sowec1-prog/litvinov-oled/include/team_logos.h

#pragma once
#include <Arduino.h>
constexpr uint8_t LOGO_W = 40;
constexpr uint8_t LOGO_H = 40;

static const uint8_t LOGO_TRI[] PROGMEM = {
  0x00, 0x20, 0x40, 0x18, 0x00, 0x00, 0x81, 0xC7,
  0x86, 0x00, 0x01, 0x11, 0xC7, 0x11, 0x00, 0x04,
  0x61, 0xE7, 0x1C, 0xC0, 0x08, 0x78, 0x00, 0x1C,
  0x20, 0x10, 0x30, 0x7C, 0x10, 0x10, 0x27, 0x03,
  0x01, 0x80, 0x10, 0x2D, 0x08, 0x00, 0x20, 0x08,
  0x4F, 0x30, 0x00, 0x98, 0xE4, 0x86, 0x40, 0x47,
  0x04, 0xF0, 0x80, 0x80, 0x4C, 0x02, 0xD2, 0x30,
  0x00, 0xFC, 0x62, 0x40, 0x39, 0x01, 0x7D, 0xC1,
  0x01, 0x72, 0x3F, 0xFF, 0x90, 0x9D, 0x72, 0x39,
  0xCF, 0xF0, 0x90, 0x00, 0x30, 0x3F, 0xF0, 0x10,
  0x01, 0xC3, 0xFB, 0x60, 0x40, 0x03, 0x86, 0x65,
  0xB4, 0x40, 0x0E, 0x1E, 0x04, 0xFC, 0x4E, 0x38,
  0x04, 0x04, 0xF8, 0x58, 0x00, 0x04, 0x06, 0xF8,
  0x5E, 0x04, 0x00, 0x01, 0xF0, 0x4C, 0x24, 0x00,
  0x03, 0xF6, 0x40, 0x74, 0x00, 0x0F, 0xFC, 0x00,
  0x52, 0x00, 0x3F, 0xF8, 0x9C, 0x72, 0x03, 0xFF,
  0xB0, 0xBC, 0x20, 0x03, 0xFF, 0x30, 0x39, 0x01,
  0x00, 0xFC, 0xF1, 0x19, 0x8C, 0x80, 0x31, 0xF2,
  0x02, 0x9E, 0x40, 0x06, 0x04, 0x02, 0x4A, 0x20,
  0x0F, 0x08, 0x04, 0x4C, 0x10, 0x00, 0x13, 0x04,
  0x20, 0x4C, 0x00, 0x63, 0x88, 0x10, 0xE1, 0xC7,
  0x01, 0x90, 0x09, 0xF0, 0x08, 0x38, 0x20, 0x04,
  0x62, 0x08, 0x78, 0x40, 0x02, 0x06, 0x1C, 0x78,
  0x80, 0x01, 0x87, 0x1E, 0x03, 0x00, 0x00, 0x40,
  0x12, 0x04, 0x00, 0x00, 0x18, 0x00, 0x30, 0x00,
};

static const uint8_t LOGO_LIT[] PROGMEM = {
  0x00, 0x30, 0xFE, 0x18, 0x00, 0x00, 0xC7, 0xFF,
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
  0x5B, 0xFF, 0xFC, 0x80, 0x0D, 0x3F, 0xFF, 0xF1,
  0x00, 0x3D, 0x20, 0x00, 0x03, 0x70, 0x7A, 0x40,
  0x00, 0x1E, 0x81, 0xFE, 0x9F, 0xFF, 0xFF, 0x0F,
  0xF4, 0xBF, 0xFF, 0xFC, 0x3F, 0xE8, 0x7F, 0xFF,
  0xF3, 0xFF, 0xD0, 0x23, 0xFF, 0x87, 0xFF, 0xA0,
};
