sowec1-prog/litvinov-oled/include/hcverva_logo.h

#pragma once
#include <Arduino.h>

// Oficiální znak HC VERVA Litvínov, převedený do 1bitové podoby pro SH1106.
static constexpr uint8_t HC_VERVA_LOGO_WIDTH = 54;
static constexpr uint8_t HC_VERVA_LOGO_HEIGHT = 54;
static const uint8_t HC_VERVA_LOGO[] PROGMEM = {
  0x00, 0x00, 0x00, 0xFE, 0x00, 0x00, 0x00, 0x00, 0x00, 0x1E, 0x03, 0xE0, 0x00, 0x00,
  0x00, 0x00, 0xE0, 0x00, 0x1C, 0x00, 0x00, 0x00, 0x03, 0x80, 0x8E, 0x03, 0x00, 0x00,
  0x00, 0x06, 0x06, 0x8F, 0x21, 0x80, 0x00, 0x00, 0x18, 0x06, 0x8C, 0x38, 0x60, 0x00,
  0x00, 0x20, 0x03, 0x8C, 0x2C, 0x30, 0x00, 0x00, 0x40, 0x03, 0x9A, 0x78, 0x88, 0x00,
  0x00, 0x8E, 0x01, 0x8E, 0x78, 0xC4, 0x00, 0x01, 0x08, 0x00, 0x00, 0x59, 0xB2, 0x00,
  0x02, 0x09, 0x00, 0x00, 0x01, 0xE1, 0x00, 0x06, 0x0D, 0x83, 0xFF, 0x03, 0xC0, 0x80,
  0x04, 0x07, 0x0C, 0x00, 0xC1, 0x80, 0x80, 0x08, 0xE2, 0x30, 0x00, 0x30, 0x0E, 0x40,
  0x19, 0x70, 0x40, 0x00, 0x08, 0x3E, 0x60, 0x11, 0xF8, 0x80, 0x00, 0x04, 0x3C, 0x20,
  0x30, 0xE1, 0x00, 0x00, 0x02, 0x18, 0x30, 0x20, 0x32, 0x00, 0x00, 0x01, 0x18, 0x10,
  0x20, 0x04, 0x00, 0x00, 0x01, 0x80, 0x10, 0x40, 0x04, 0x00, 0x00, 0x01, 0x80, 0x08,
  0x40, 0x08, 0x00, 0x00, 0x02, 0x40, 0x08, 0x40, 0x08, 0x00, 0x00, 0x06, 0x40, 0x08,
  0x40, 0x10, 0x00, 0x00, 0x0C, 0x20, 0x08, 0xC0, 0x10, 0x00, 0x00, 0x0C, 0x20, 0x08,
  0x80, 0x10, 0x00, 0x00, 0x38, 0x20, 0x04, 0x80, 0x10, 0x1F, 0xFF, 0xF0, 0x20, 0x04,
  0x80, 0x10, 0x1F, 0x03, 0xF0, 0x20, 0x04, 0xFF, 0x9E, 0x00, 0xFC, 0x3F, 0xE7, 0xFC,
  0xFF, 0x9E, 0x00, 0x00, 0x7F, 0xE7, 0xFC, 0xFF, 0x9C, 0x00, 0x00, 0x7F, 0xEF, 0xFC,
  0x7F, 0xD8, 0xFF, 0xFF, 0xFF, 0xEF, 0xF8, 0x7F, 0xC9, 0xFF, 0xFF, 0xFF, 0xCF, 0xF8,
  0x7F, 0xC9, 0xFF, 0xFF, 0xFF, 0xCF, 0xF8, 0x7F, 0xEB, 0xFF, 0xFF, 0xFF, 0xDF, 0xF8,
  0x7F, 0xE7, 0xFF, 0xFF, 0xFF, 0x9F, 0xF8, 0x3F, 0xF7, 0xFF, 0xFF, 0xFF, 0xBF, 0xF0,
  0x3F, 0xF3, 0xFF, 0xFF, 0xFF, 0x3F, 0xF0, 0x3F, 0xF9, 0xFF, 0xFF, 0xFE, 0x7F, 0xF0,
  0x1F, 0xFC, 0xFF, 0xFF, 0xFC, 0xFF, 0xE0, 0x1F, 0xEE, 0x7F, 0xFF, 0xF9, 0xDF, 0xE0,
  0x0F, 0xC7, 0x3F, 0xFF, 0xF3, 0x8F, 0xC0, 0x07, 0x9F, 0x8F, 0xFF, 0xC7, 0x07, 0x80,
  0x07, 0x1F, 0xE1, 0xFE, 0x1F, 0x03, 0x80, 0x03, 0x0C, 0xF8, 0x00, 0x78, 0xC3, 0x00,
  0x01, 0x9C, 0xFF, 0x07, 0xF0, 0xF6, 0x00, 0x00, 0xF9, 0x87, 0xFF, 0x92, 0x7C, 0x00,
  0x00, 0x71, 0x80, 0xB6, 0x18, 0x38, 0x00, 0x00, 0x3B, 0xC4, 0x32, 0x0C, 0x70, 0x00,
  0x00, 0x1F, 0x9C, 0x32, 0x0E, 0xE0, 0x00, 0x00, 0x07, 0x9C, 0x33, 0x0F, 0x80, 0x00,
  0x00, 0x03, 0xFC, 0x73, 0x2F, 0x00, 0x00, 0x00, 0x00, 0xFE, 0x73, 0xFC, 0x00, 0x00,
  0x00, 0x00, 0x1F, 0xFF, 0xE0, 0x00, 0x00, 0x00, 0x00, 0x00, 0xFC, 0x00, 0x00, 0x00,
};
